Zeberdyber/nECU_EE110/Firmware/nECU/Inc/nECU_Knock.h

/**
 ******************************************************************************
 * @file    nECU_Knock.h
 * @brief   This file contains all the function prototypes for
 *          the nECU_Knock.c file
 */
#ifndef _NECU_KNOCK_H_
#define _NECU_KNOCK_H_

#ifdef __cplusplus
extern "C"
{
#endif

/* Includes */
#include "main.h"
#include "nECU_types.h"
#include "nECU_adc.h"
#include "nECU_tim.h"
#include "nECU_table.h"

/* Definitions */
#define KNOCK_BETA 10        // value in [%/s] of knock retard regression
#define KNOCK_LEVEL 5        // multiplier how much will steps will be taken for severe knock
#define KNOCK_STEP 5         // in % how much should be retarded in one step
#define KNOCK_FREQUENCY 8000 // in Hz

    /* Knock detection */
    bool nECU_Knock_Start(void);                          // initialize and start
    void nECU_Knock_ADC_Callback(uint16_t *input_buffer); // periodic callback
    void nECU_Knock_UpdatePeriodic(void);                 // function to calculate current retard value
    static void nECU_Knock_DetectMagn(void);              // function to detect knock based on ADC input
    static void nECU_Knock_Evaluate(float *magnitude);    // check if magnitude is of knock range
    bool nECU_Knock_Stop(void);                           // stop
    uint8_t *nECU_Knock_GetPointer(void);                 // returns pointer to knock retard percentage

#ifdef __cplusplus
}
#endif

#endif /* _NECU_KNOCK_H_ */
